lambtor/Phaser/userSettings.py

class UserSettings:
    def __init__(self):
        self.Frequency = 0
        self.Volume = 3
        # self.Orientation = 0
        self.BeamBrightIndex = 3
        self.SettingBrightIndex = 3
        self.FreqSup = 0
        self.SleepTimer = 1
